chengzhag/ball_on_big_plate/OpenCV_raspberry_ball_locating/OpenCV_raspberry_remote_camera_calibration/matlab/2.jpg

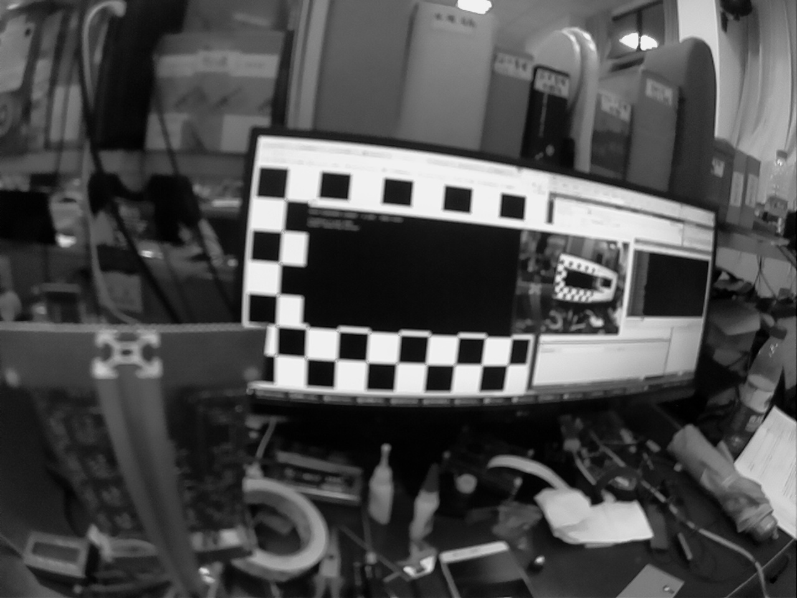
OpenCV_raspberry_ball_locating/OpenCV_raspberry_remote_camera_calibration/matlab/2.jpg
