chengzhag/ball_on_big_plate/stm32_ball_on_plate/ebox_stm32f103RCT6_VS/ebox_stm32f103RCT6_VS/common/edriver/SFUD/docs/zh/images/RTT_ART_WiFi.jpg

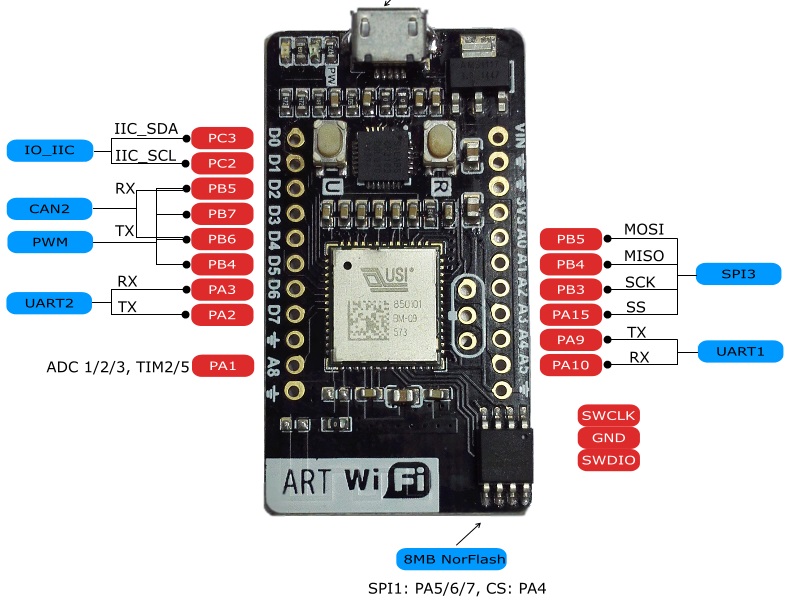
stm32_ball_on_plate/ebox_stm32f103RCT6_VS/ebox_stm32f103RCT6_VS/common/edriver/SFUD/docs/zh/images/RTT_ART_WiFi.jpg
